KonradMcClure/SDR_Receiver/images/CorrectedBandpassFilter.png

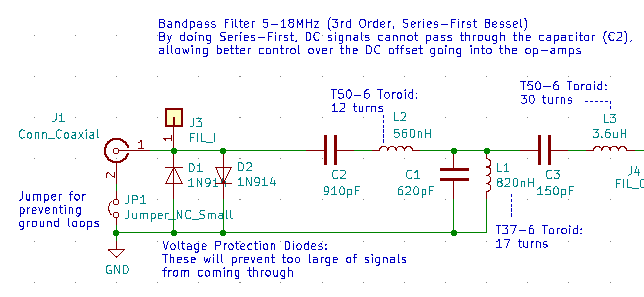
images/CorrectedBandpassFilter.png
