KonradMcClure/SDR_Receiver/images/CorrectedFilterSim.png

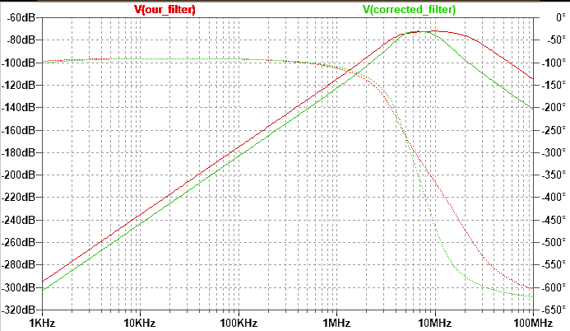
images/CorrectedFilterSim.png
