KonradMcClure/SDR_Receiver/images/Diagrams/OpAmpBuffer.jpg

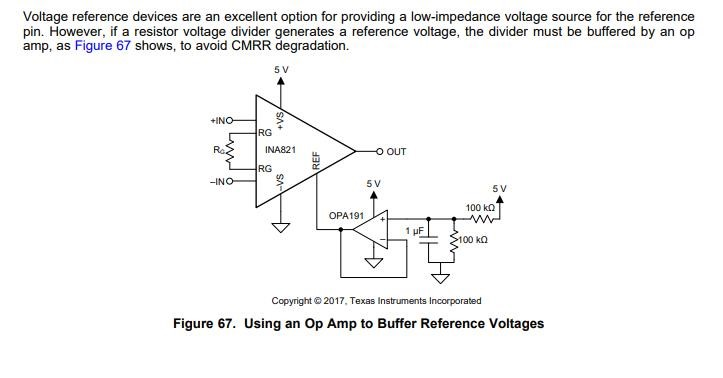
images/Diagrams/OpAmpBuffer.jpg
