KonradMcClure/SDR_Receiver/images/PCBLayout_Rev2.png

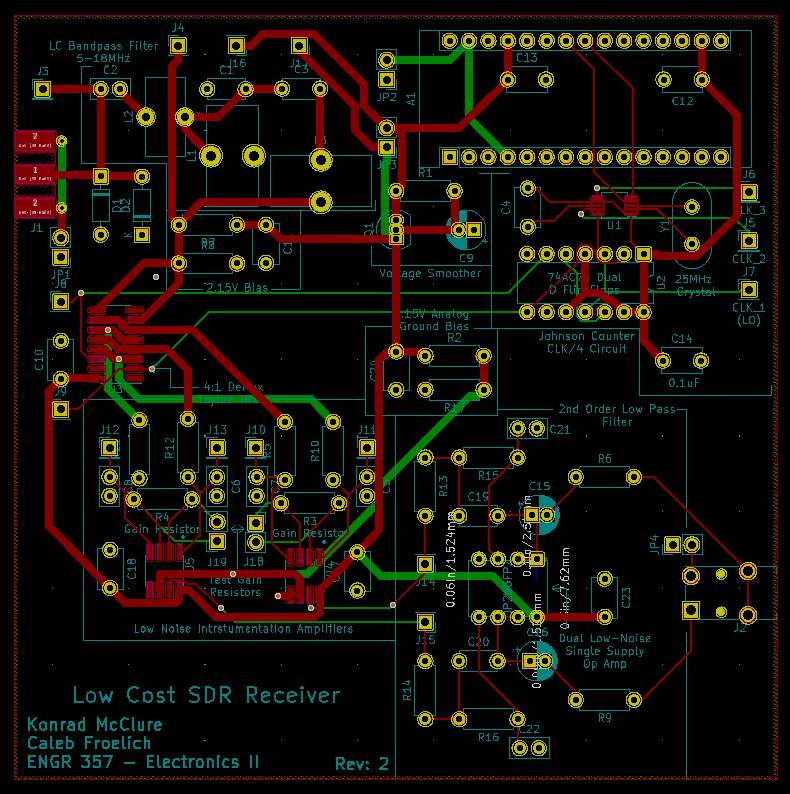
images/PCBLayout_Rev2.png
