KonradMcClure/SDR_Receiver/images/Prototypes/Proto_Rev2-5_Full.jpg

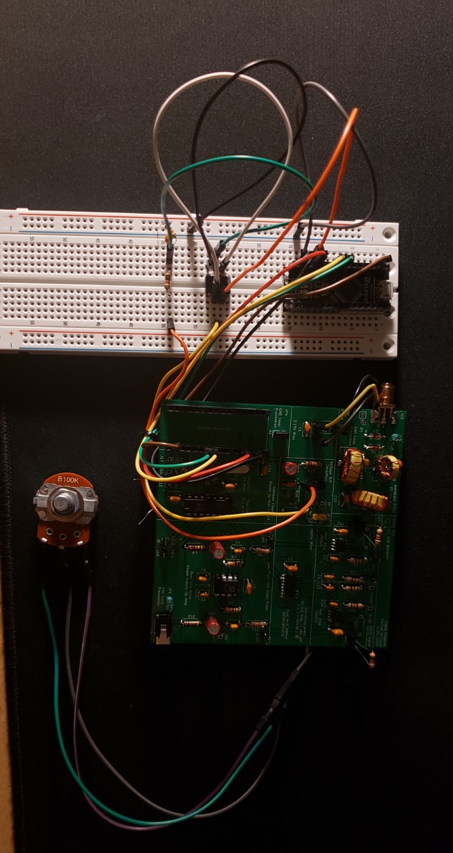
images/Prototypes/Proto_Rev2-5_Full.jpg
