KonradMcClure/SDR_Receiver/images/Prototypes/Proto_Rev2_BandpassFilter.jpg

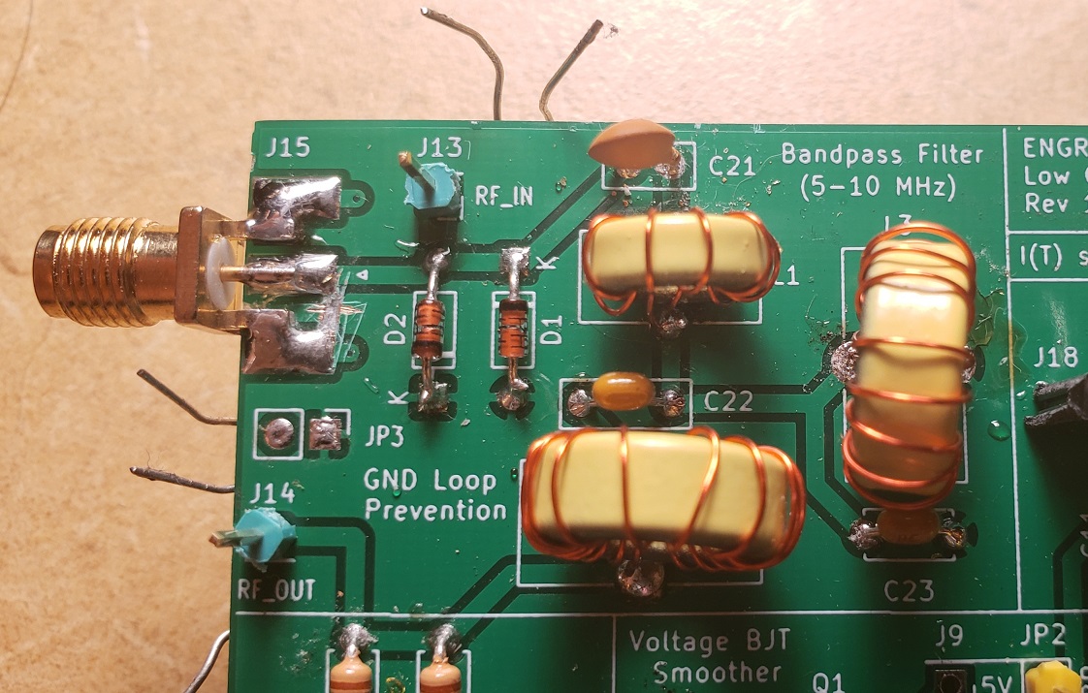
images/Prototypes/Proto_Rev2_BandpassFilter.jpg
