KonradMcClure/SDR_Receiver/images/Prototypes/Proto_Rev2_Digital.jpg

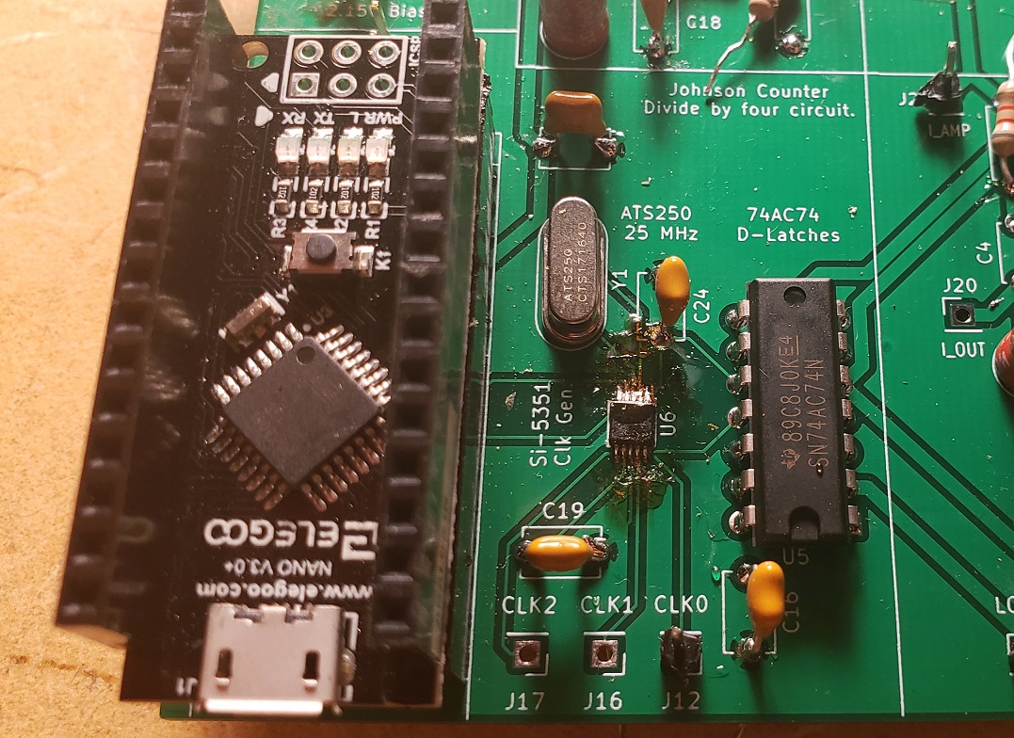
images/Prototypes/Proto_Rev2_Digital.jpg
