KonradMcClure/SDR_Receiver/images/Prototypes/Proto_Rev2_Full.jpg

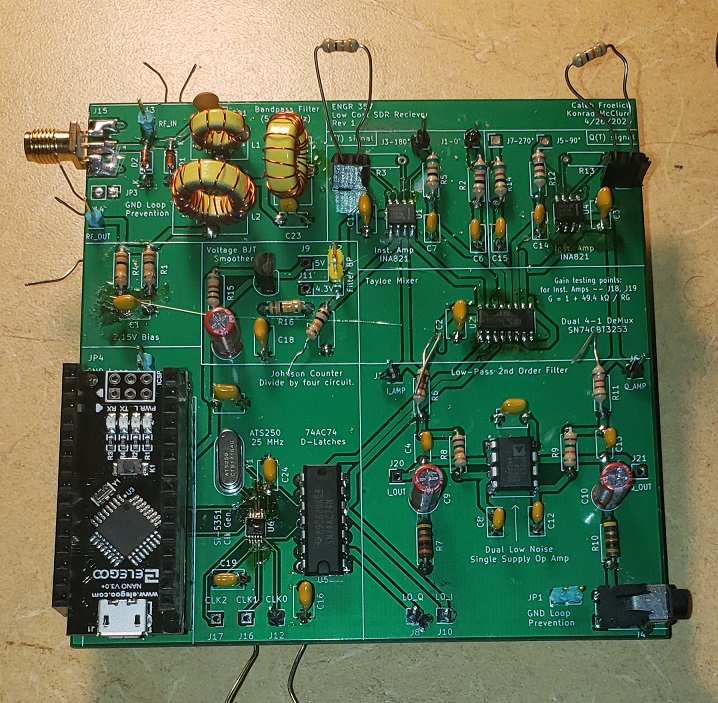
images/Prototypes/Proto_Rev2_Full.jpg
