KonradMcClure/SDR_Receiver/images/Prototypes/Proto_Rev2_InstAmps.jpg

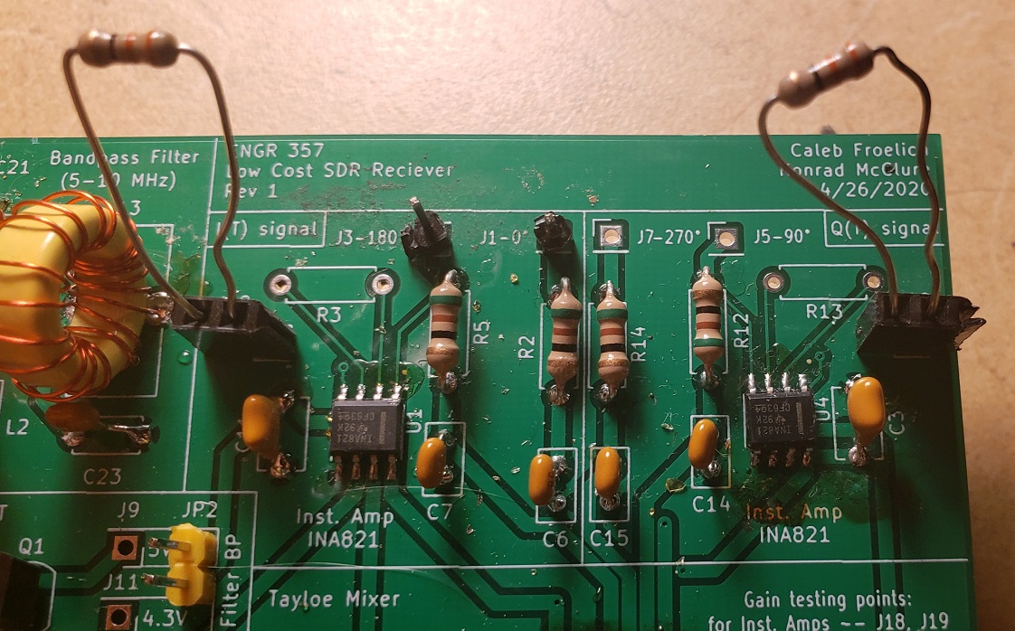
images/Prototypes/Proto_Rev2_InstAmps.jpg
