KonradMcClure/SDR_Receiver/images/Prototypes/Proto_Rev2_LowpassFilter.jpg

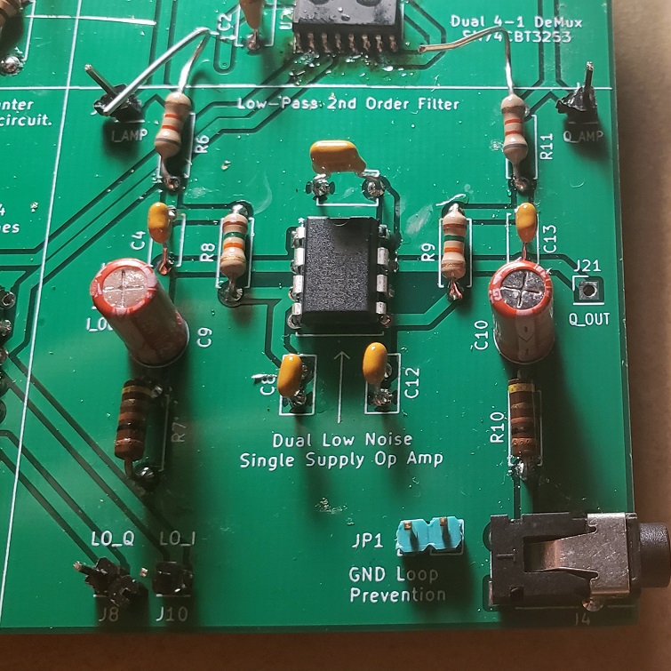
images/Prototypes/Proto_Rev2_LowpassFilter.jpg
