KonradMcClure/SDR_Receiver/images/Prototypes/Proto_Rev2_VoltageSmoother.jpg

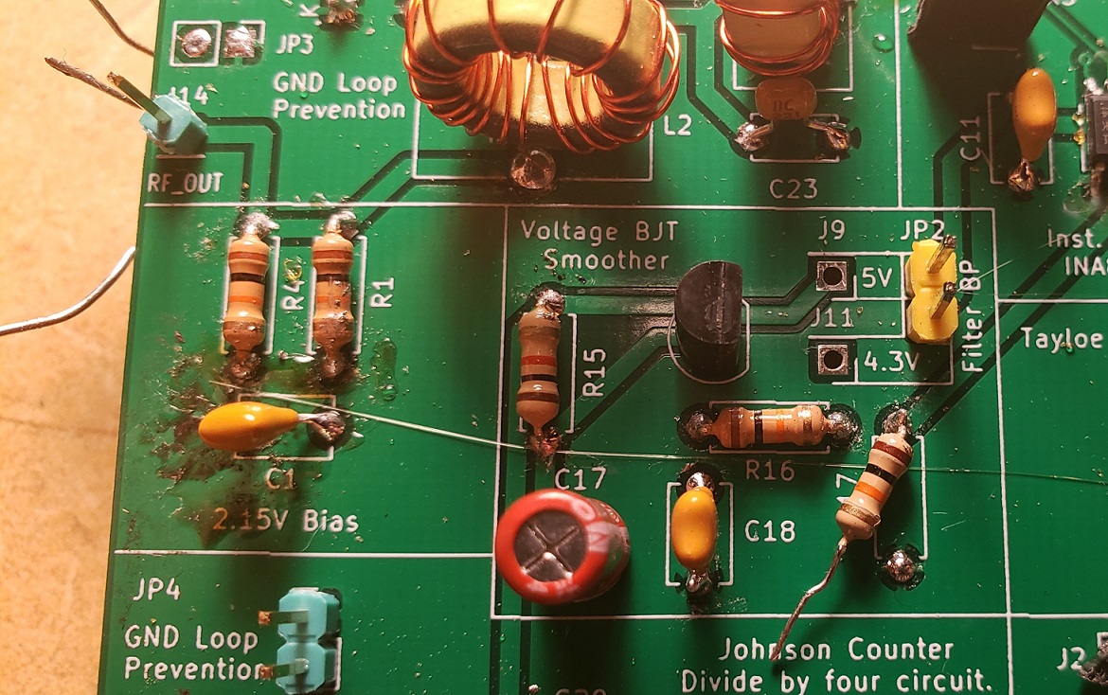
images/Prototypes/Proto_Rev2_VoltageSmoother.jpg
