KonradMcClure/SDR_Receiver/images/Schematics/Rev2_Schem_Arduino.png

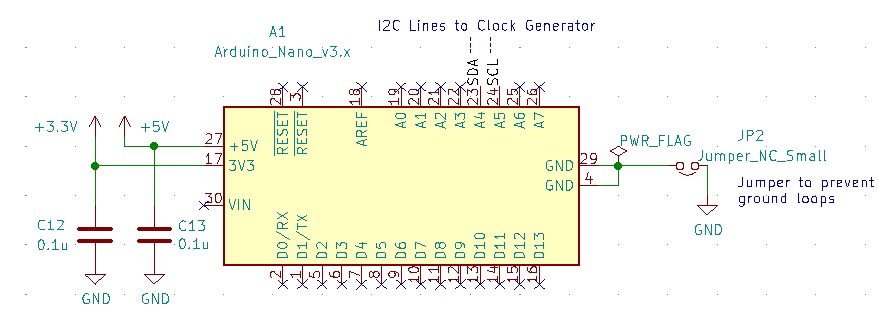
images/Schematics/Rev2_Schem_Arduino.png
