KonradMcClure/SDR_Receiver/images/Rev2CostTable.png

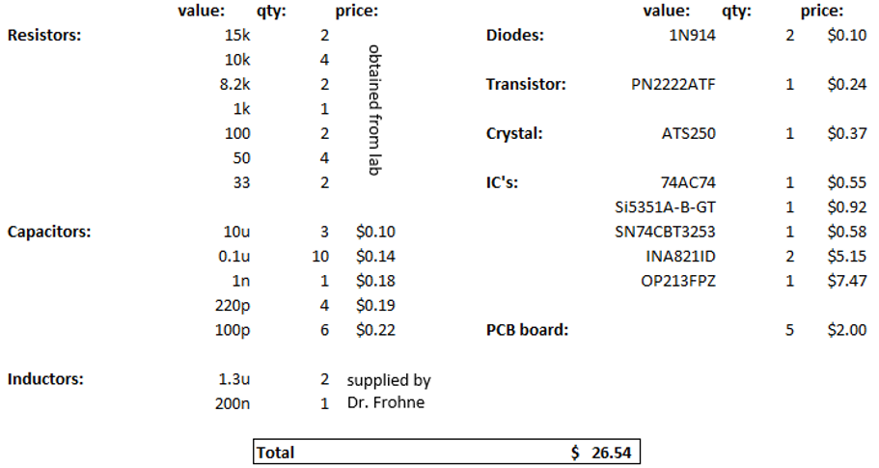
images/Rev2CostTable.png
