KonradMcClure/SDR_Receiver/images/Testing/InstTest_I-Sig_0+180deg.png

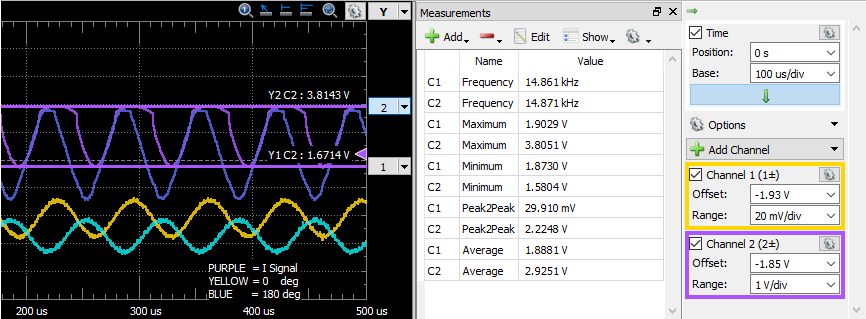
images/Testing/InstTest_I-Sig_0+180deg.png
