KonradMcClure/SDR_Receiver/images/Testing/Issue3+4_0vs90vs180vs270.png

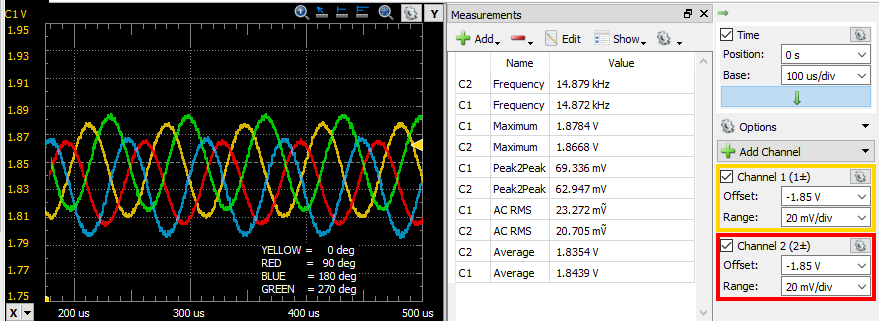
images/Testing/Issue3+4_0vs90vs180vs270.png
