KonradMcClure/SDR_Receiver/images/Testing/Issue4_0vs90.png

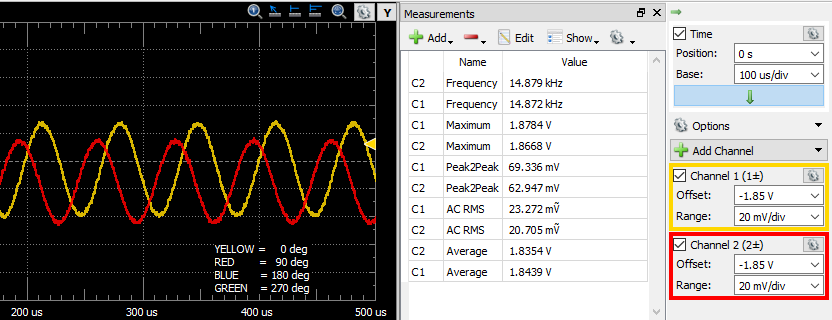
images/Testing/Issue4_0vs90.png
