KonradMcClure/SDR_Receiver/images/Testing/Issue4_0vs180.png

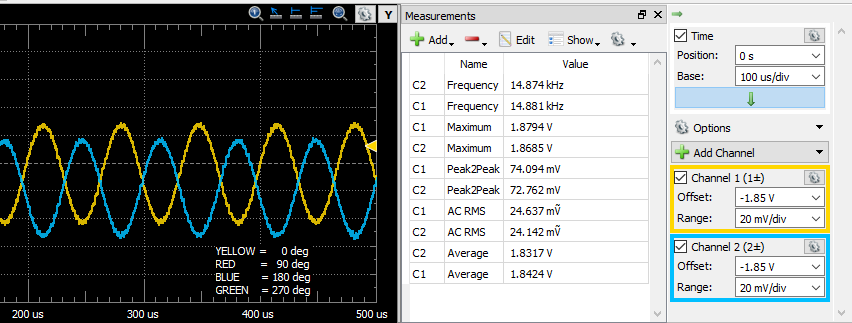
images/Testing/Issue4_0vs180.png
