KonradMcClure/SDR_Receiver/LTSpiceSims/InstAmpDesignNoLowpass.asc

C1: cap; {C_Sample}
C4: cap; 0.1µ
C5: cap; {C_Sample}
C6: cap; {C_Sample}
C7: cap; {C_Sample}
C8: cap; 0.1µ
C9: cap; 910µ
C10: cap; 620p
C11: cap; 150p
C12: cap; 0.1µ
C15: cap; 10µ
L1: ind; 1µ
L2: ind; 1µ
L3: ind; 3.6µ
R1: res; 50
R2: res; 50
R3: res; 50
R4: res; 100
R5: res; 50
R6: res; 100
R7: res; 50
R9: res; 55k
R10: res; 55k
R13: res; 50
R14: res; 10k
R15: res; 10k
R22: res; 50
R23: res; 50
R24: res; 50
R25: res; 50
R26: res; 10k
R27: res; 10k
S2: sw; MYSW
S4: sw; MYSW
S6: sw; MYSW
S7: sw; MYSW
U1: LT1167
U8: LT1167
V1: voltage; PULSE(0 1 0 0.001p 0.001p {SW_time} {4*SW_time})
V2: voltage; PULSE(0 1 {SW_time} 0.001p 0.001p {SW_time} {4*SW_time})
V3: voltage; SINE(0 5m {RF_Freq}); Rser=50
V4: voltage; 5
V5: voltage; 5
V6: voltage; PULSE(0 1 {2*SW_time} 0.001p 0.001p {SW_time} {4*SW_time})
V7: voltage; PULSE(0 1 {3*SW_time} 0.001p 0.001p {SW_time} {4*SW_time})
V8: voltage; SINE(0 5u {RF_freq})
V9: voltage; SINE(0 5u {RF_freq})
V10: voltage; SINE(0 3u {0.2*RF_freq})
V11: voltage; SINE(0 3u {2*RF_freq})
Named nets: 0, 5V, -5V, V_0_deg, V_90_deg, V_180_deg, V_270_deg, 00, 11, V_filtered, V_unfiltered, bias_pt, 01, 10, AGND, V_ideal, V_messy
.model MYSW SW(Vt=0.9 Vh=0 Ron=1 Roff=100G)
.tran 0 1m 0m 0.5u
.param RF_freq=10Meg
;op
.param C_Sample=100p
Instrumentation Amp INA821 Sim
.param LO_freq={RF_freq - 10.7k}
.param LO_period={1/LO_freq}
.param LOB_delay={LOA_delay*2}
.param LOA_delay={LO_on/2}
.param LO_on={LO_period/2}
.param SW_time={LO_period/4}
Primary Parameters
MUX Model Parameters
Simulation Commands
MUX Model Signals
Signal Source Choices
Bandpass Filter
MUX Model
Custom Models
Supply + Analog Ground
Instrumentation Amps
Input Impedence of
The Soundcard
Input Impedence of
The Soundcard
(5 - 10 MHz Passband)
Various Choices for Testing
