KonradMcClure/SDR_Receiver/LTSpiceSims/DoubleBalancedMixerTest.asc

D1: diode
D2: diode
D3: diode
D4: diode
L1: ind2; 100µ
L2: ind2; 50µ
L3: ind2; 50µ
L4: ind2; 50µ
L5: ind2; 50µ
L6: ind2; 100µ
R1: res; 1k
R2: res; 10
R3: res; 10
R4: res; 1k
S1: sw; MYSW
V1: voltage; SINE(0 1 10Meg)
V2: voltage; SINE(0 0.1 3Meg)
V3: voltage; SINE(0 1 10k)
V4: voltage; PULSE(-1 1 0 0.01m 0.01m 0.166665m 0.3333m)
Named nets: 0, LO, RF
.tran 0 1m 0
.model MYSW SW(Ron=1 Roff=1Meg Vt=0 Vh=0
K1 L1 L2 L3 1
K2 L4 L5 L6 1
