KonradMcClure/SDR_Receiver/LTSpiceSims/BandpassFilter.asc

C14: cap; 620pF
C15: cap; 618pF
C16: cap; 943pF
C17: cap; 220p
C18: cap; 1n
C19: cap; 220p
C20: cap; 144.5pF
C21: cap; 910pF
C22: cap; 150pF
C23: cap; 620pF
C24: cap; 910pF
C25: cap; 150pF
L14: ind; 820nH
L15: ind; 537nH
L16: ind; 3.507µH
L17: ind; 1.3µ
L18: ind; 200n
L19: ind; 1.3µ
L20: ind; 820nH
L21: ind; 560nH
L22: ind; 3.6µH
L23: ind; 867nH
L24: ind; 576nH
L25: ind; 3.6µH
R9: res; 50
R10: res; 50
R11: res; 50
R12: res; 50
R13: res; 50
R14: res; 50
R15: res; 50
R16: res; 50
V5: voltage; 5V; AC 0.5m
V6: voltage; 5V; AC 0.5m
V7: voltage; 5V; AC 0.5m
V8: voltage; 5V; AC 0.5m
Named nets: 0, Our_Filter, Corrected_FilterTolerance, Corrected_OurCores, Corrected_FilterExact
.ac dec 100 1k 100Meg
Out Incorrect Rev 2
Bandpass Filter Values
Regeneration with 
correct values
5% tolerance
Min Cap: 1pF
Min Ind: 1nH
BandpassFilter.asc
Simulation for testing our bandpass filters.
All the filters were generated at https://rf-tools.com/lc-filter/
5% tolerance
Min Cap: 1pF
Min Ind: 1nH
Values of Inductors based
on our T37-6 and T50-6
toroidial cores
