KonradMcClure/SDR_Receiver/LTSpiceSims/LowpassFilter.asc

C3: cap; 220p
C4: cap; 100p
R2: res; 50
R3: res; 8.2k
R4: res; 15k
U1: OP213
V1: voltage; ""; AC 1; Rser=50
V2: voltage; 5V
Named nets: 0, 5V, Vout
Input Impedence of
The Soundcard
.ac dec 1000 100 100Meg
Simulation Commands
Lowpass Filter Sim
2nd Order Lowpass filter with a 
100kHz cutoff Frequency
