KonradMcClure/SDR_Receiver/LTSpiceSims/MUXModel.asc

A1: inv
A2: inv
R1: res; 50
R2: res; 50
R3: res; 50
R4: res; 50
S1: sw; MYSW
S2: sw; MYSW
S3: sw; MYSW
S4: sw; MYSW
S5: sw; MYSW
S6: sw; MYSW
S7: sw; MYSW
S8: sw; MYSW
V1: voltage; PULSE(0 1 75n 1p 1p 100n 200n)
V2: voltage; PULSE(0 1 25n 1p 1p 100n 200n)
V3: voltage; SINE(0 1 10Meg)
Named nets: 0, 00, 01, 11, 10
.model MYSW SW(Vt=0.9 Vh=0 Ron=1 Roff=100G)
.tran 0 1u 0 0.01u
Multiplexer Model
One design of a possible model for a multiplexer. In the overall model, we found it
was easier to just use four signal sources for four switches rather than two sources
for eight switches
