KonradMcClure/SDR_Receiver/LTSpiceSims/NoiseSim.asc

C1: cap; {C_Sample}
C4: cap; 0.1µ
C5: cap; {C_Sample}
C6: cap; {C_Sample}
C7: cap; {C_Sample}
C8: cap; 0.1µ
C9: cap; 910µ
C10: cap; 620p
C11: cap; 150p
C15: cap; 10µ
L1: ind; 1µ
L2: ind; 1µ
L3: ind; 3.6µ
R1: res; 50
R2: res; 50
R4: res; 100
R5: res; 50
R6: res; 100
R9: res; 55k
R10: res; 55k
R13: res; 50
R22: res; 50
R23: res; 50
R24: res; 50
R25: res; 50
R26: res; 10k
R27: res; 10k
U1: LT1167
U8: LT1167
V3: voltage; SINE(0 5m {RF_Freq}); Rser=50
V4: voltage; 5
V5: voltage; 5
V8: voltage; SINE(0 5u {RF_freq})
V9: voltage; SINE(0 5u {RF_freq})
Named nets: 0, 5V, -5V, V_unfiltered, V_filtered, 01, 10, AGND, V_ideal, V_messy, vout
.model MYSW SW(Vt=0.9 Vh=0 Ron=1 Roff=100G)
;tran 0 1m 0m 0.5u
.param RF_freq=10Meg LO_freq={RF_freq - 10.7k} LO_period={1/LO_freq} LOB_delay={LOA_delay*2} LOA_delay={LO_on/2} LO_on={LO_period/2} SW_time={LO_period/4}
;op
.param C_Sample=100p
.noise V(vout) V3 dec 100 10 100Meg
